Markahofmeister/ShowHerb/media/images/Control-Box-Footprint.jpg

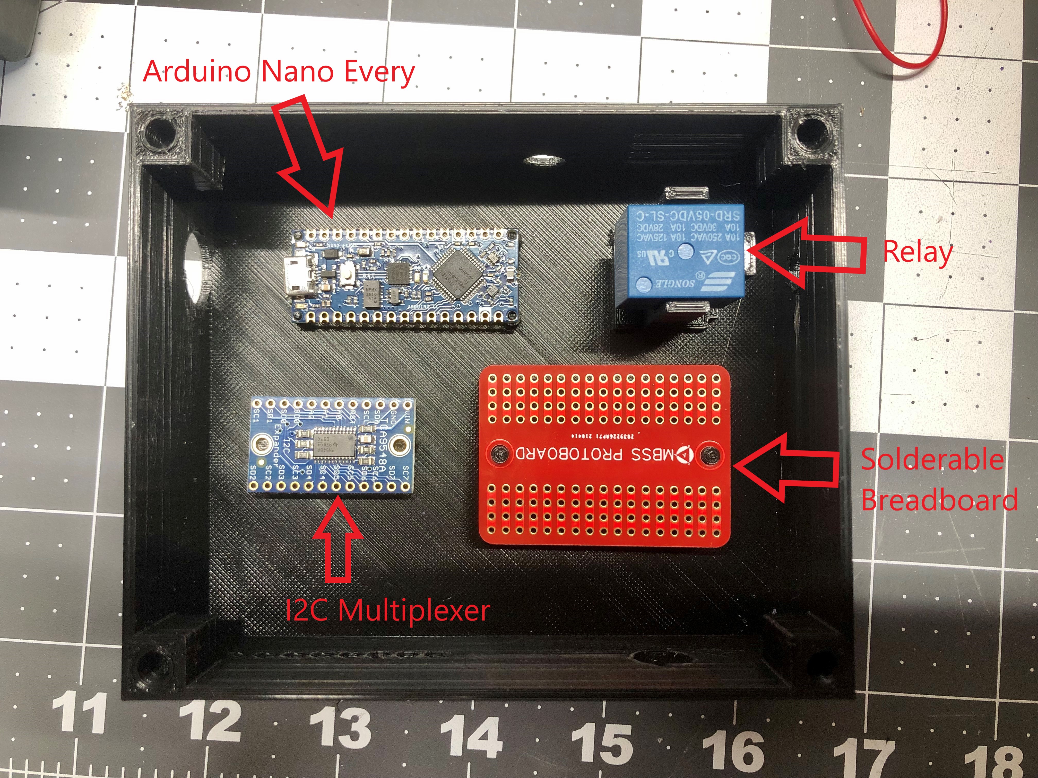
media/images/Control-Box-Footprint.jpg
