Markahofmeister/ShowHerb/media/images/Control-Box-Plugs.jpg

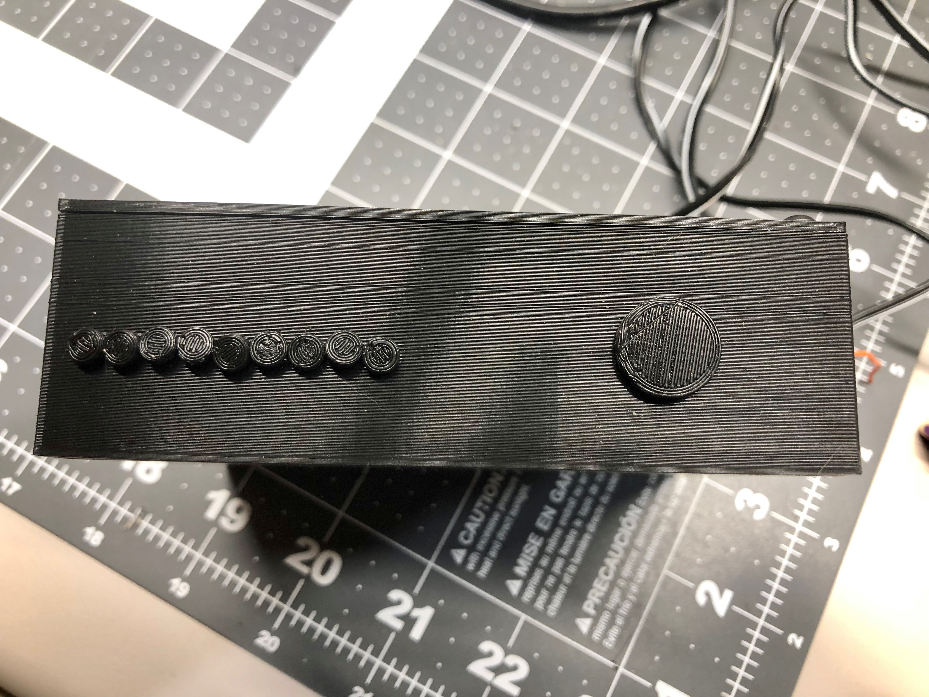
media/images/Control-Box-Plugs.jpg
