Markahofmeister/ShowHerb/media/images/Photocell-case-v1.jpg

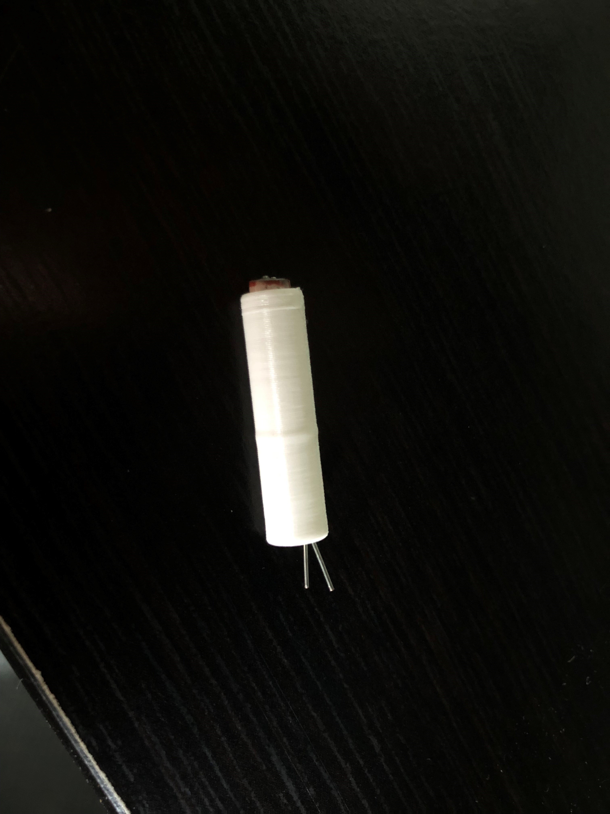
media/images/Photocell-case-v1.jpg
