Markahofmeister/ShowHerb/media/images/Photocell-case-v2.jpg

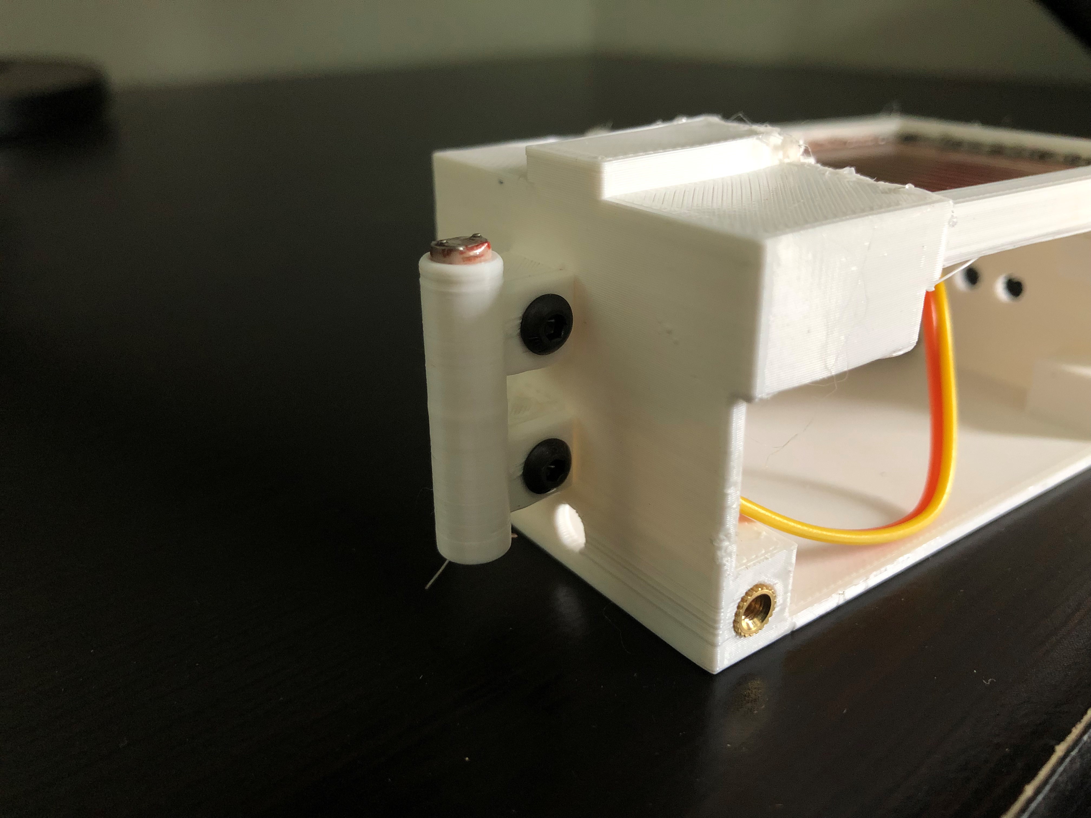
media/images/Photocell-case-v2.jpg
