Markahofmeister/ShowHerb/media/images/Rain-Sensor-Case.jpg

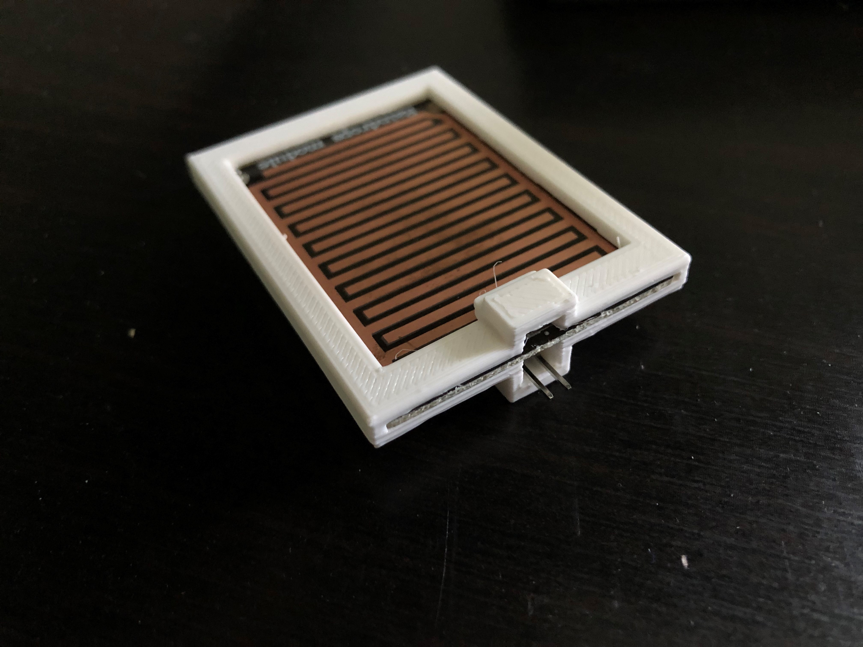
media/images/Rain-Sensor-Case.jpg
