Markahofmeister/ShowHerb/media/images/Rain-Sensor-PCB.jpg

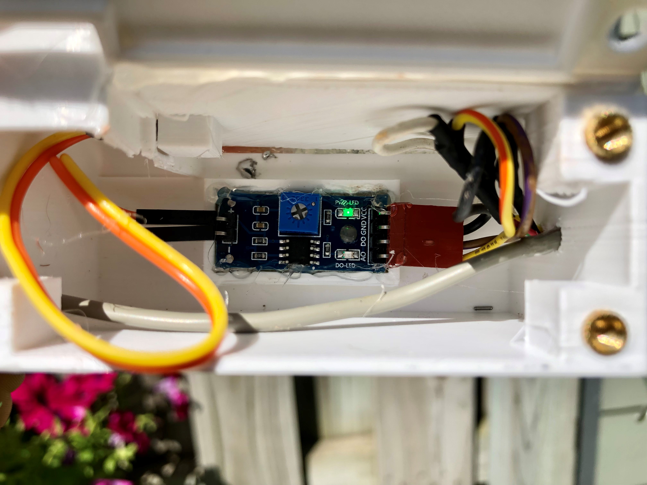
media/images/Rain-Sensor-PCB.jpg
