Markahofmeister/ShowHerb/media/images/Sensors-Box.jpg

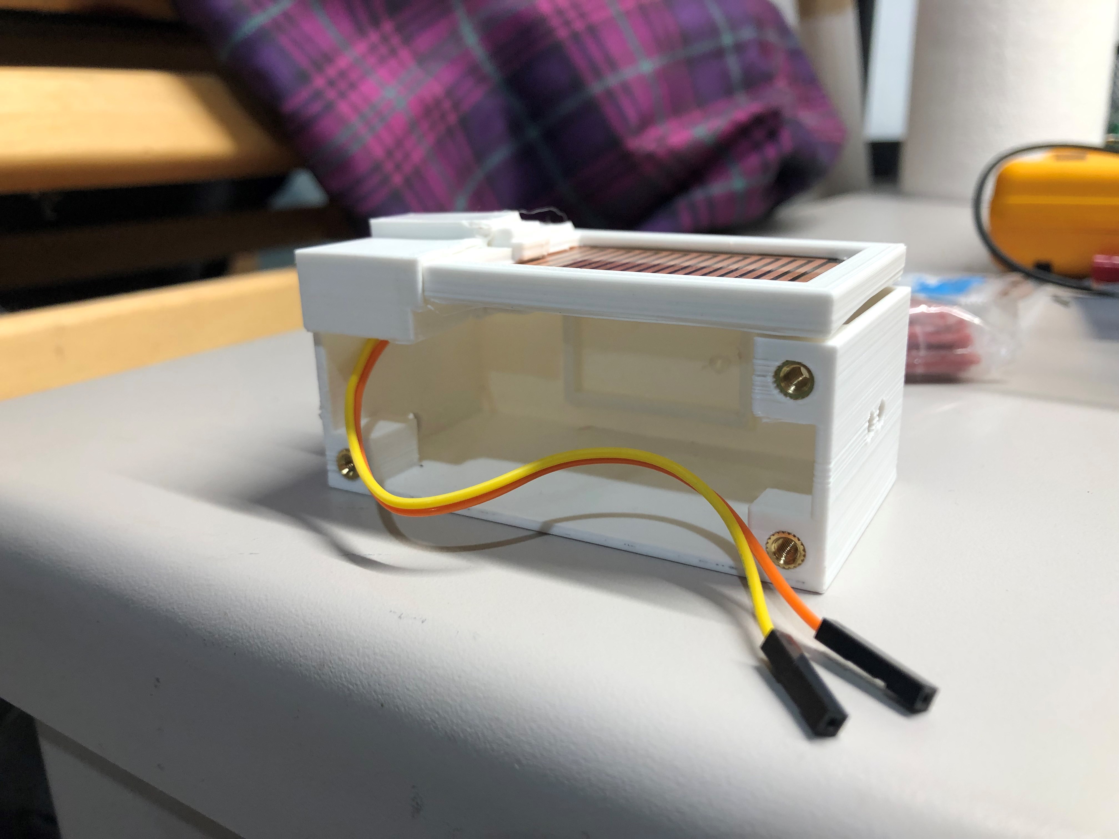
media/images/Sensors-Box.jpg
