Markahofmeister/ShowHerb/media/images/Soil-Sensor-1.jpg

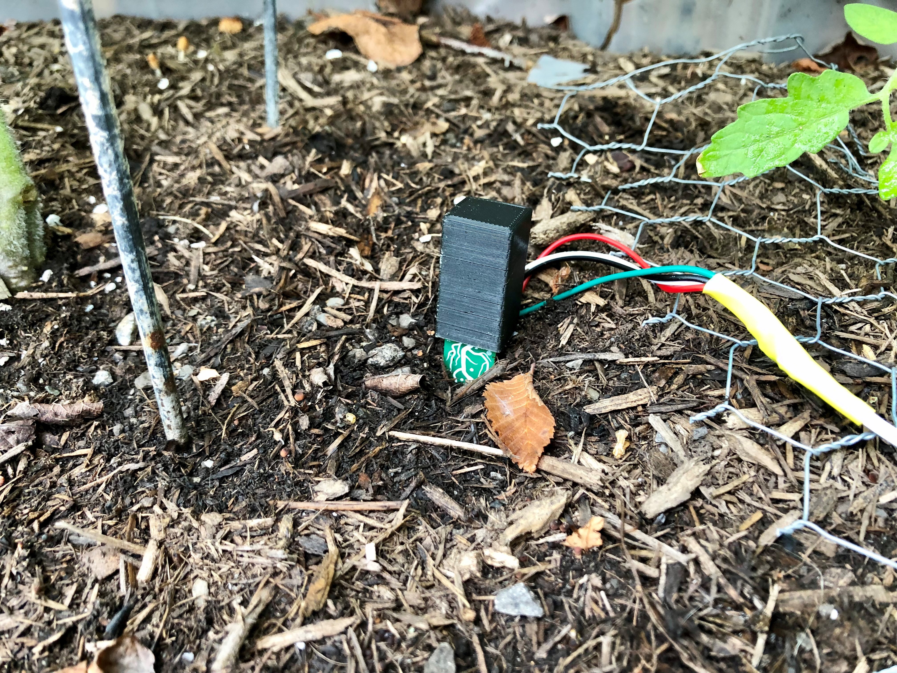
media/images/Soil-Sensor-1.jpg
