Markahofmeister/ShowHerb/media/images/Soil-Sensor.jpg

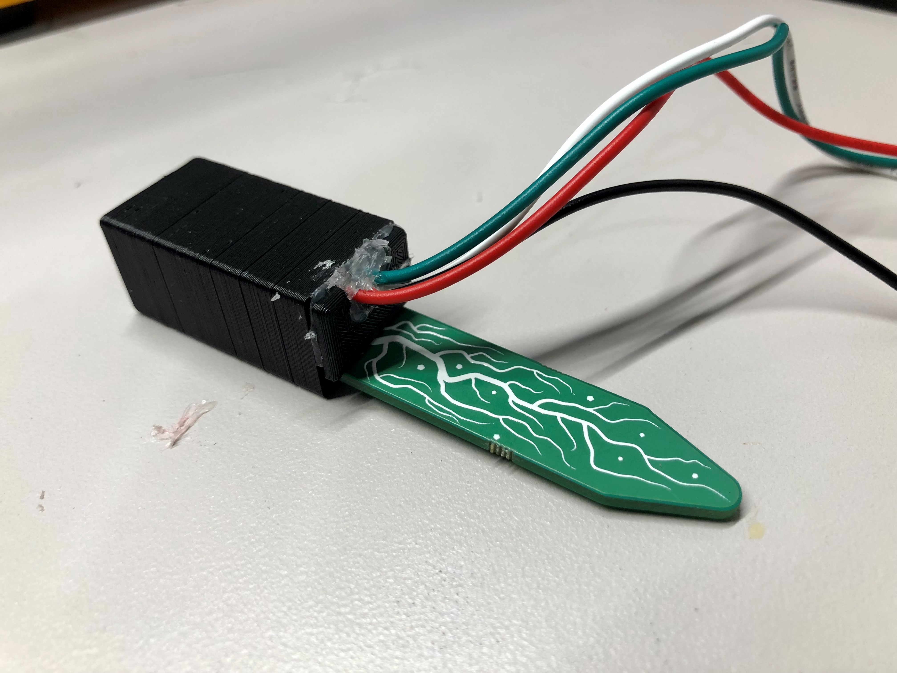
media/images/Soil-Sensor.jpg
