Markahofmeister/ShowHerb/media/images/Storage-Box-Closed.jpg

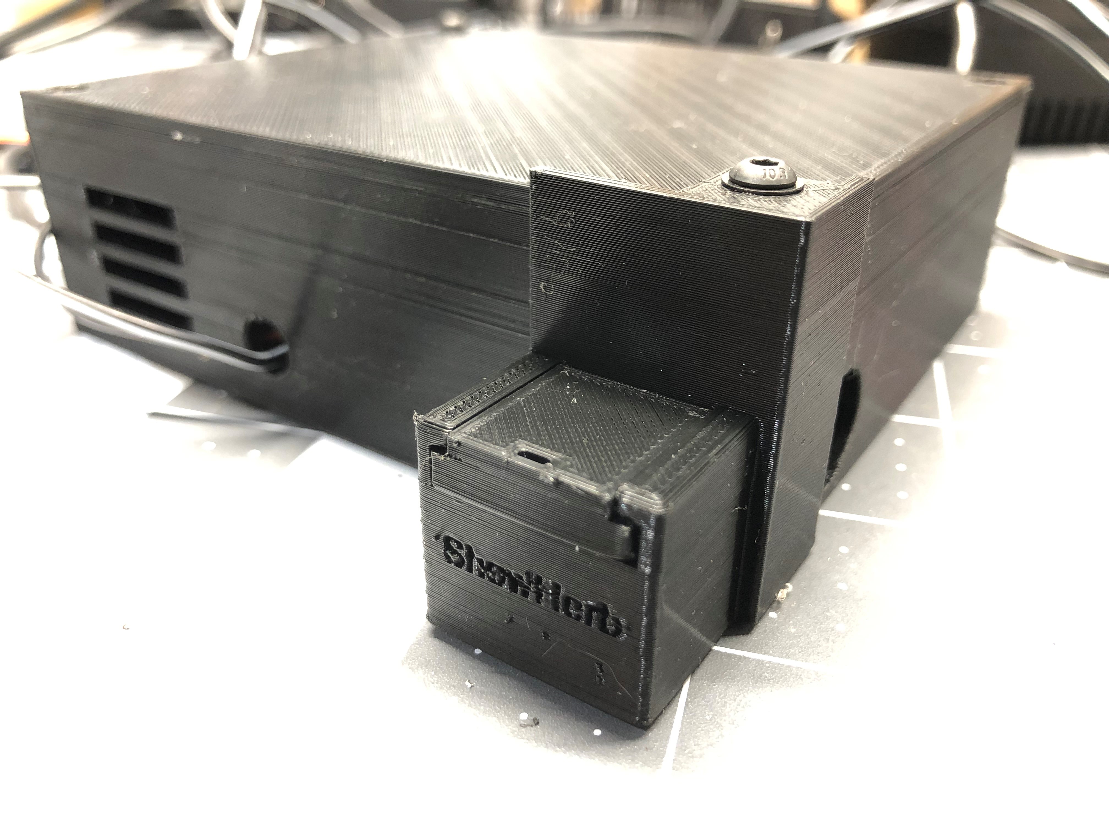
media/images/Storage-Box-Closed.jpg
