Markahofmeister/ShowHerb/media/images/Storage-Box-Open.jpg

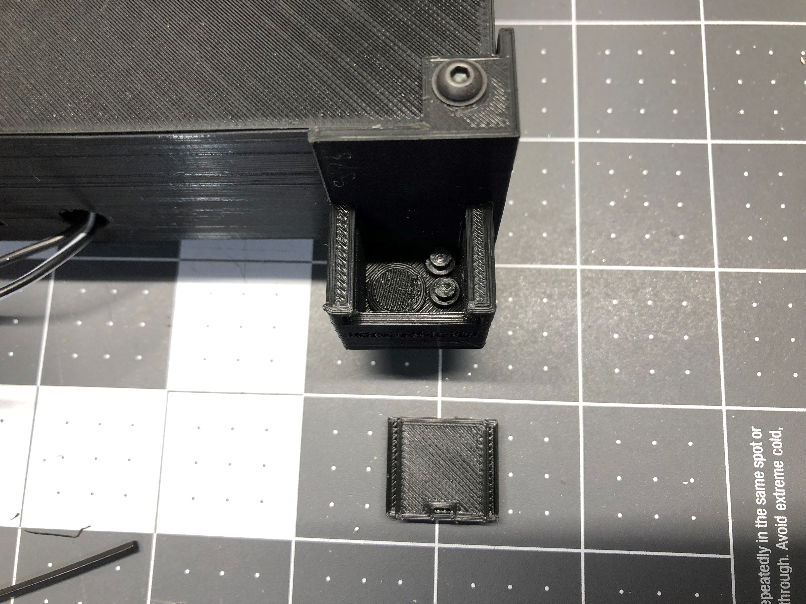
media/images/Storage-Box-Open.jpg
