Markahofmeister/ShowHerb/media/images/Wired-Control-Box.jpg

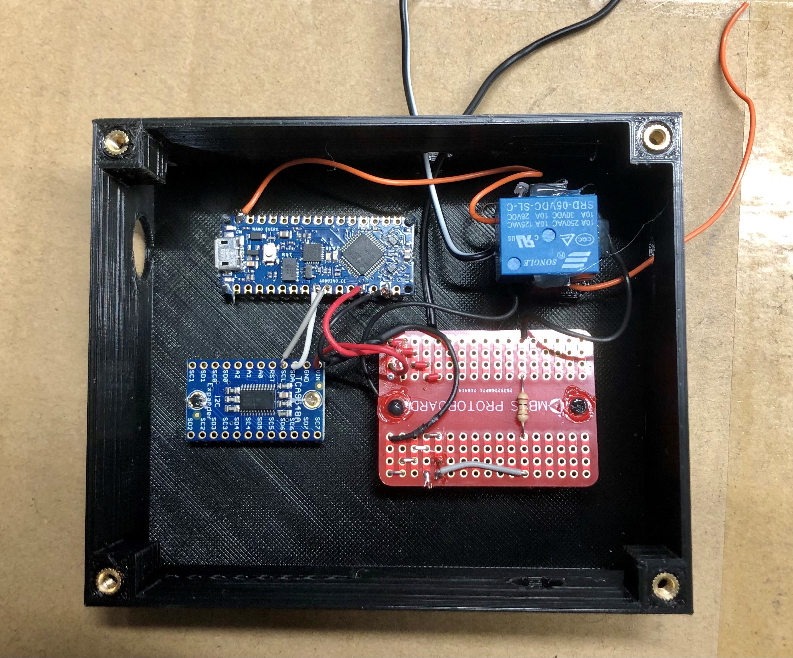
media/images/Wired-Control-Box.jpg
