Markahofmeister/ShowHerb/media/system-diagrams/SystemDiagram-V1.png

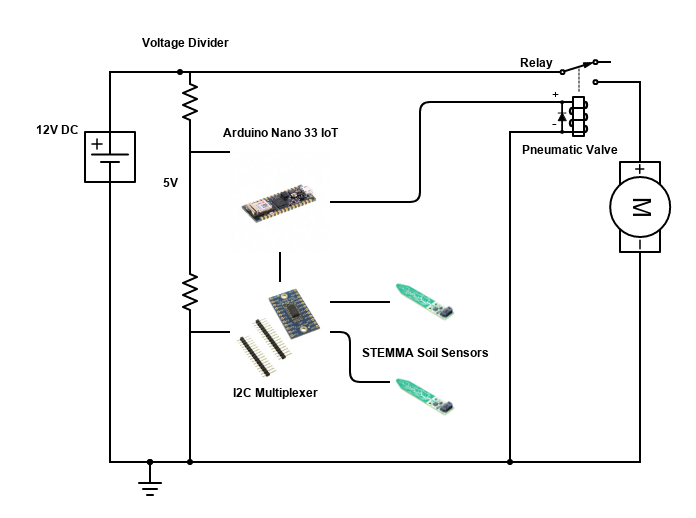
media/system-diagrams/SystemDiagram-V1.png
