Markahofmeister/ShowHerb/media/system-diagrams/SystemDiagram-V2.png

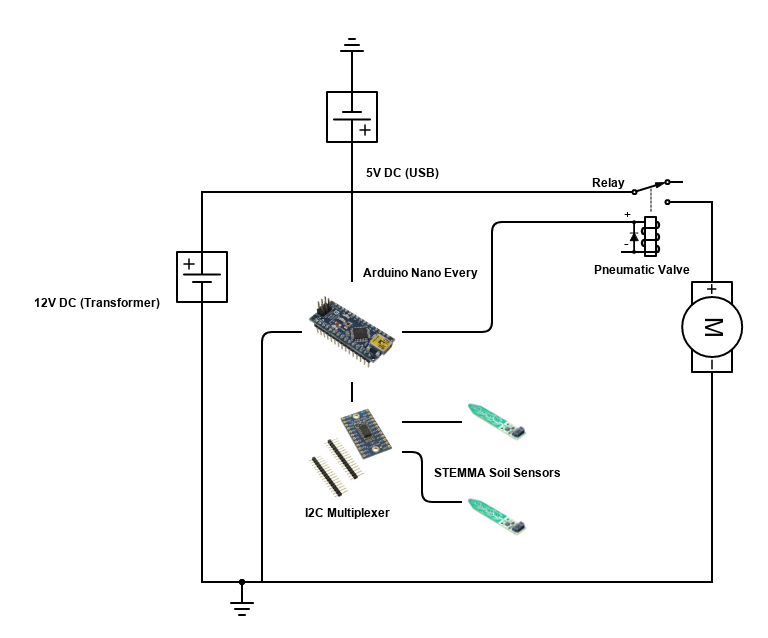
media/system-diagrams/SystemDiagram-V2.png
