Markahofmeister/ShowHerb/media/system-diagrams/SystemDiagram-V3.png

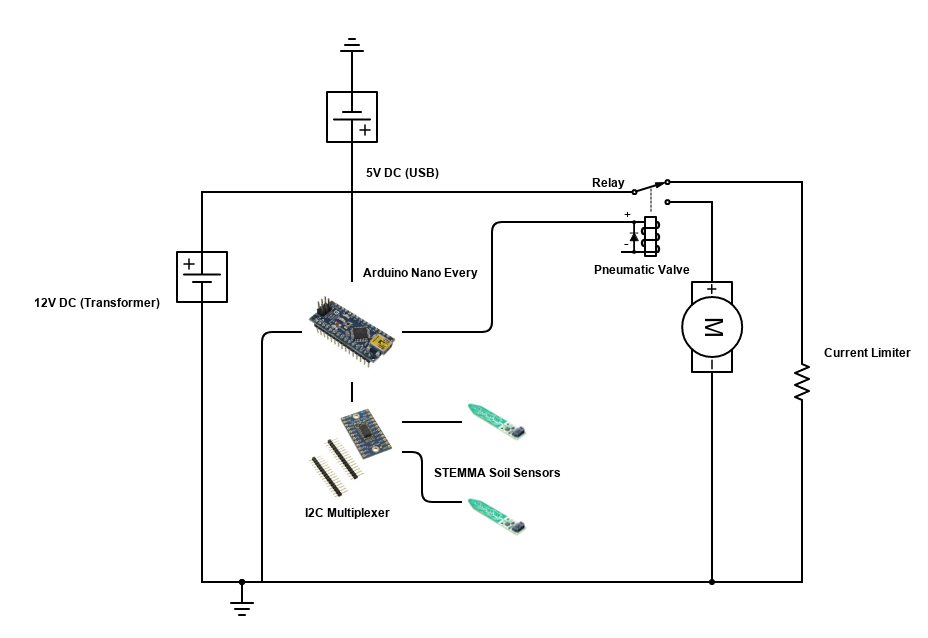
media/system-diagrams/SystemDiagram-V3.png
