Markahofmeister/ShowHerb/media/system-diagrams/SystemDiagram-V5.png

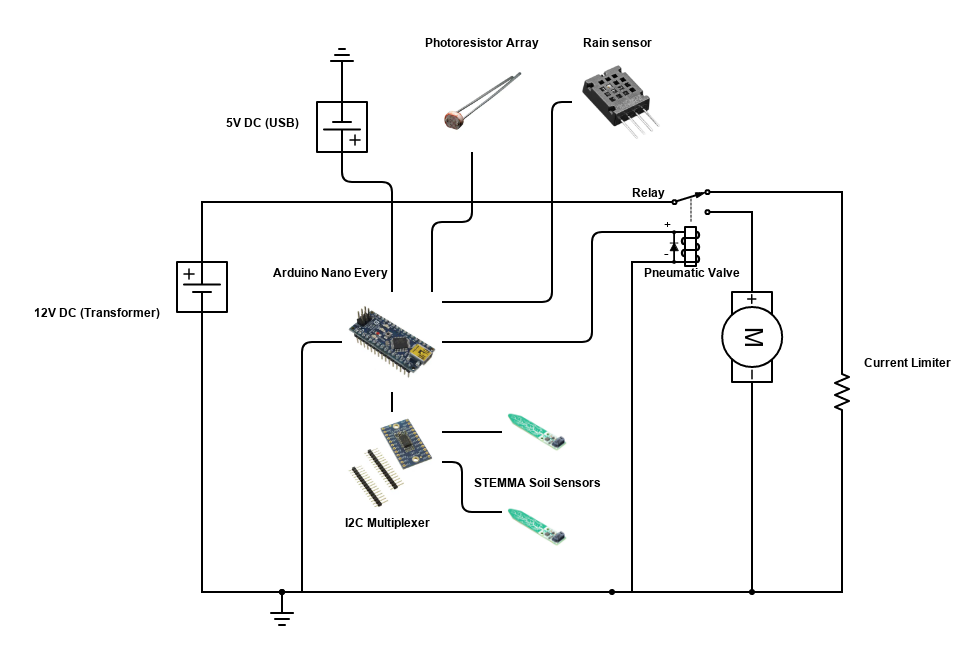
media/system-diagrams/SystemDiagram-V5.png
