Markahofmeister/ShowHerb/media/system-diagrams/SystemDiagram-V6.png

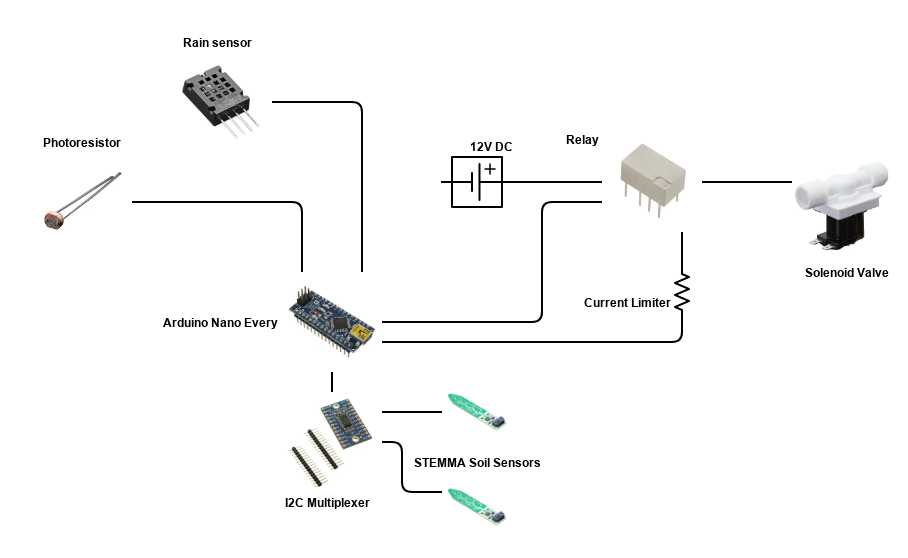
media/system-diagrams/SystemDiagram-V6.png
