Markahofmeister/ShowHerb/fab-Files/Stemma-Models/CoverPlug-v2.stl

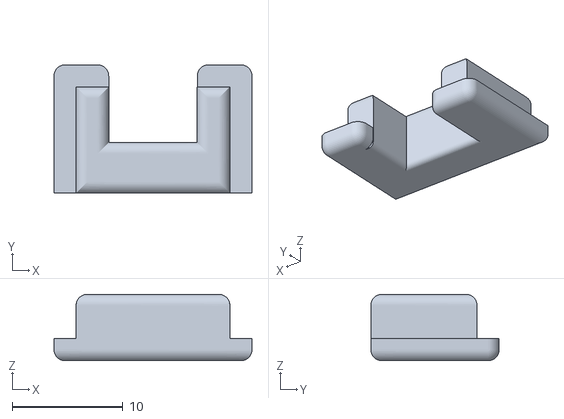
[picture p38: CAD file, 2021-07-27, an earlier design]
fab-Files/Stemma-Models/CoverPlug-v2.stl
17.9 x 11.6 x 6.00
