Markahofmeister/ShowHerb/fab-Files/Storage-Box/StorageBox-v1.stl

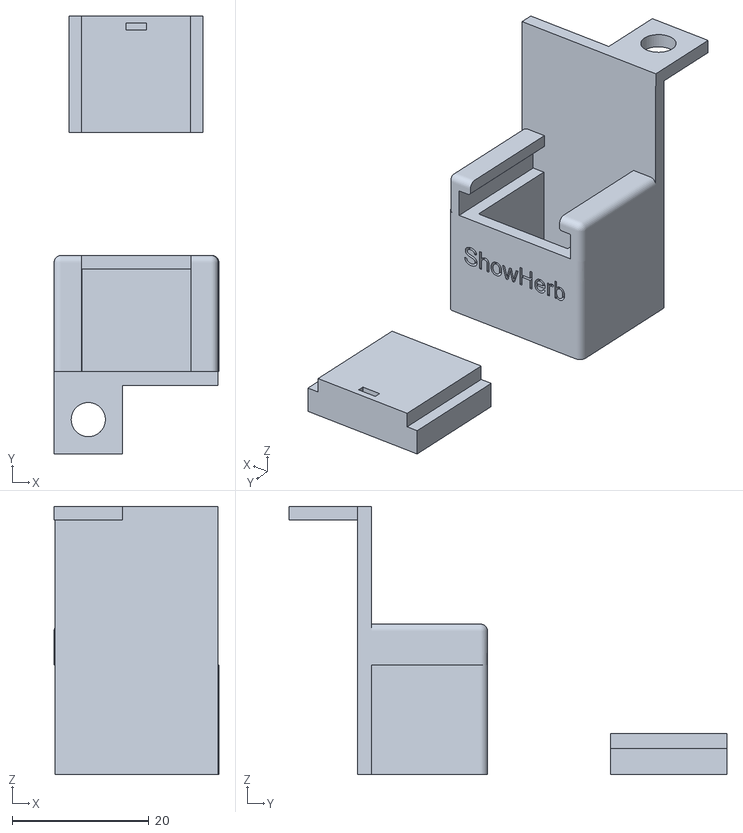
[picture p39: CAD file, 2021-08-03, an earlier design]
fab-Files/Storage-Box/StorageBox-v1.stl
24.1 x 64.0 x 39.2
