Markahofmeister/ShowHerb/fab-Files/Text/Text-v1.stl

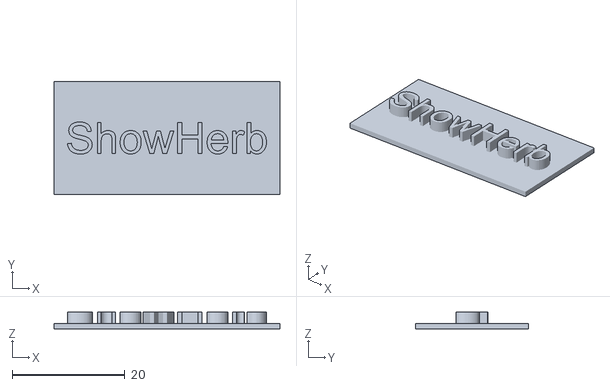
[picture p40: CAD file, 2021-08-03, an earlier design]
fab-Files/Text/Text-v1.stl
40.0 x 20.0 x 3.00
