Markahofmeister/ShowHerb/media/images/Soil-Sensor-Testing.jpg

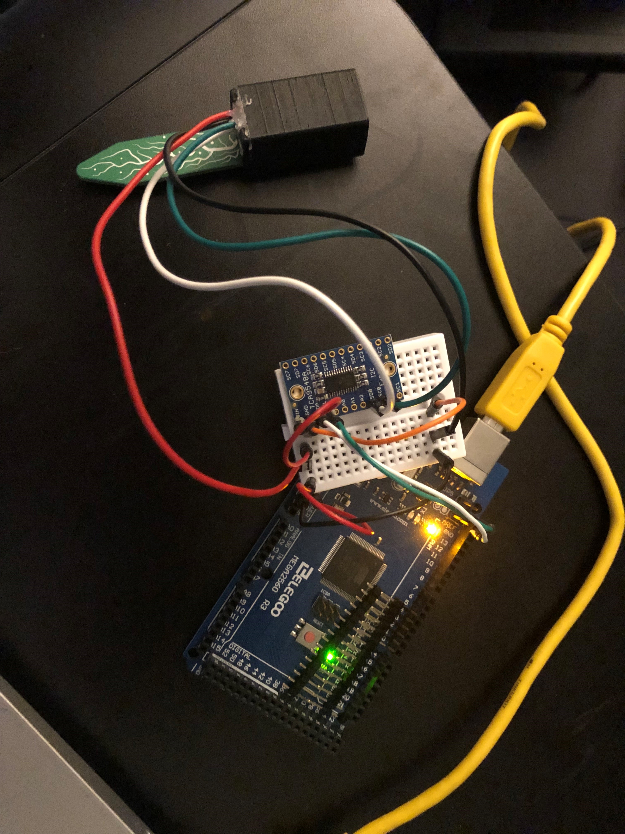
media/images/Soil-Sensor-Testing.jpg
