Markahofmeister/ShowHerb/ShowHerb-Schematic/ShowHerb-Schematic.kicad_pcb

## KiCad design cad/cpld-alu.kicad_sch

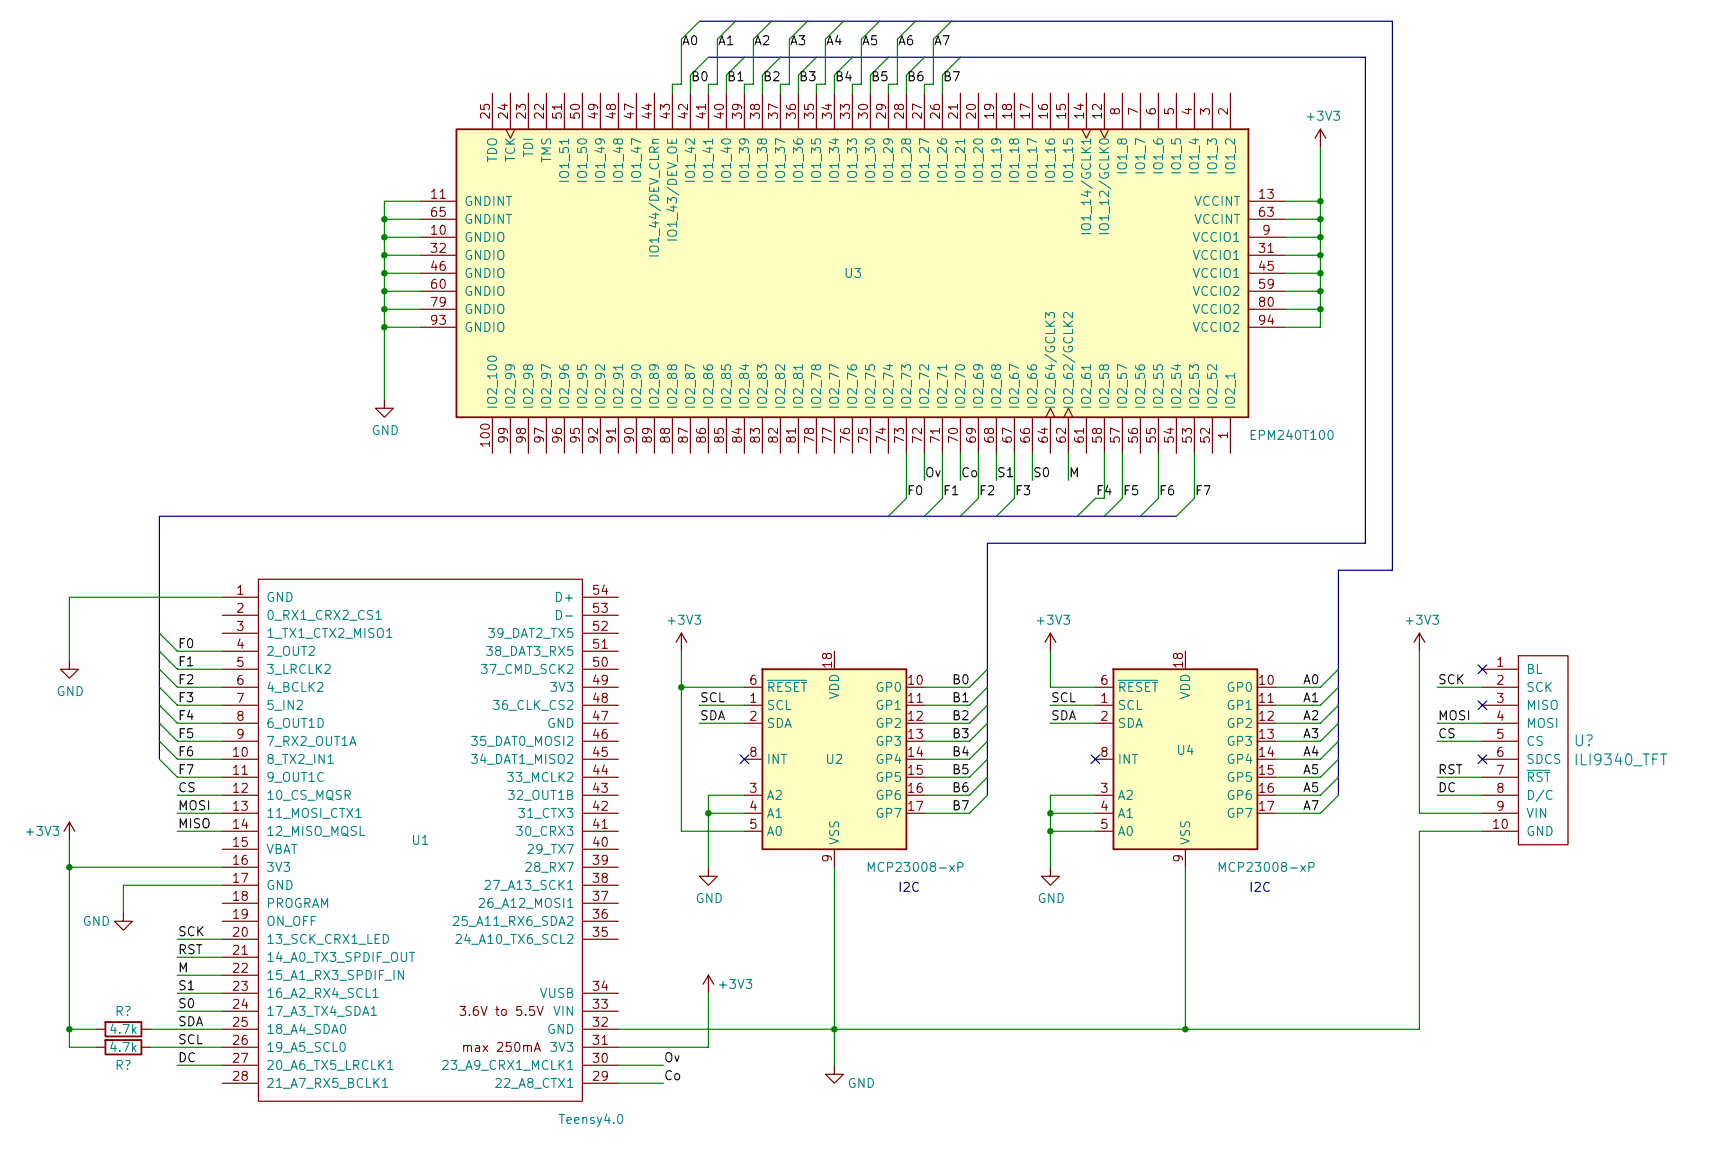
[picture p42: schematic cpld-alu.kicad_sch]

Parts:
U1: Teensy4.0
U2, U4: MCP23008-xP; DIP-18_W7.62mm
U3: EPM240T100; LQFP-100_14x14mm_P0.5mm

Connections:
+3V3: U1.16 (3V3), U1.31 (3V3), U2.5 (A0), U2.6 (~RESET), U3.9 (VCCIO1), U3.13 (VCCINT), U3.31 (VCCIO1), U3.45 (VCCIO1), U3.59 (VCCIO2), U3.63 (VCCINT), U3.80 (VCCIO2), U3.94 (VCCIO2), U4.6 (~RESET)
A0: U3.43 (IO1_43/DEV_OE), U4.10 (GP0)
A1: U3.41 (IO1_41), U4.11 (GP1)
A2: U3.39 (IO1_39), U4.12 (GP2)
A3: U3.37 (IO1_37), U4.13 (GP3)
A4: U3.35 (IO1_35), U4.14 (GP4)
A5: U3.33 (IO1_33), U4.15 (GP5), U4.16 (GP6)
A6: U3.29 (IO1_29)
A7: U3.27 (IO1_27), U4.17 (GP7)
B0: U2.10 (GP0), U3.42 (IO1_42)
B1: U2.11 (GP1), U3.40 (IO1_40)
B2: U2.12 (GP2), U3.38 (IO1_38)
B3: U2.13 (GP3), U3.36 (IO1_36)
B4: U2.14 (GP4), U3.34 (IO1_34)
B5: U2.15 (GP5), U3.30 (IO1_30)
B6: U2.16 (GP6), U3.28 (IO1_28)
B7: U2.17 (GP7), U3.26 (IO1_26)
CS: U1.12 (10_CS_MQSR)
Co: U1.29 (22_A8_CTX1), U3.70 (IO2_70)
DC: U1.27 (20_A6_TX5_LRCLK1)
F0: U1.4 (2_OUT2), U3.73 (IO2_73)
F1: U1.5 (3_LRCLK2), U3.71 (IO2_71)
F2: U1.6 (4_BCLK2), U3.69 (IO2_69)
F3: U1.7 (5_IN2), U3.67 (IO2_67)
F4: U1.8 (6_OUT1D), U3.58 (IO2_58)
F5: U1.9 (7_RX2_OUT1A), U3.57 (IO2_57)
F6: U1.10 (8_TX2_IN1), U3.55 (IO2_55)
F7: U1.11 (9_OUT1C), U3.53 (IO2_53)
GND: U1.1 (GND), U1.17 (GND), U1.32 (GND), U2.3 (A2), U2.4 (A1), U2.9 (VSS), U3.10 (GNDIO), U3.11 (GNDINT), U3.32 (GNDIO), U3.46 (GNDIO), U3.60 (GNDIO), U3.65 (GNDINT), U3.79 (GNDIO), U3.93 (GNDIO), U4.3 (A2), U4.4 (A1), U4.5 (A0), U4.9 (VSS)
M: U1.22 (15_A1_RX3_SPDIF_IN), U3.62 (IO2_62/GCLK2)
MISO: U1.14 (12_MISO_MQSL)
MOSI: U1.13 (11_MOSI_CTX1)
Ov: U1.30 (23_A9_CRX1_MCLK1), U3.72 (IO2_72)
RST: U1.21 (14_A0_TX3_SPDIF_OUT)
S0: U1.24 (17_A3_TX4_SDA1), U3.66 (IO2_66)
S1: U1.23 (16_A2_RX4_SCL1), U3.68 (IO2_68)
SCK: U1.20 (13_SCK_CRX1_LED)
SCL: U1.26 (19_A5_SCL0), U2.1 (SCL), U4.1 (SCL)
SDA: U1.25 (18_A4_SDA0), U2.2 (SDA), U4.2 (SDA)

Notes on the sheet:
I2C
